Nexusnui/Animated-Mini-BlueBrixx-Gate/Code/animated-gate/data/PuddleLoop.gif

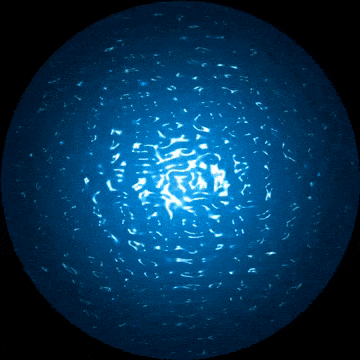
Code/animated-gate/data/PuddleLoop.gif
